impatrq/OIB_Sleep/Documentos/historias de usuarios .docx

Frente de la tarjeta | Reverso de la tarjeta
Comodidad Como Paciente que debe permanecer acostado por un largo tiempo Puedo usando materiales para que no se sientan los tubos de calefaccion y refrigeracion Para Permanecer cómodo durante la estancia en cama Criterios de Aceptación - Dado que quiero permanecer comodo en la cama - Cuando tenga que estar acostado - Entonces Los materiales de la cama van a ser óptimos y los tubos se pondrán en una posición para que no se sientan. | Detalles: - Los tubos deben ser flexibles para acomodarlos - La estructura de la cama tiene que mantenerse de buena calidad.
Display Como enfermero/a Puedo ver el estado del paciente Para poder controlar como esta Criterios de Aceptación - Dado que quiero ver como esta el paciente - Cuando lo este cuidando - Entonces puedo ver los datos de pulsaciones y temperatura en una display | Detalles: - Los datos se obtendran de la pico - Va a ser un display chico que pueda mostar los valores
Temperatura Como Persona mayor Puedo regular la temperatura del colchón Para ayudar a mi temperatura corporal que tiene menor regulación Criterios de Aceptación - Dado que necesito apoyo con la regulación de temperatura - Cuando duermo - Entonces La regulacion de temperatura del colchón me ayudara | Detalles: - La calefacción y refrigeración debe causar mínimo daño al colchón para que tenga una larga vida útil - La temperatura se poder regular automáticamente y manualmente
Diabetes Como persona con diabetes que afecta la circulación Puedo tener una temperatura elevada del colchón Para mejorar mi circulación en el cuerpo Criterios de Aceptación - Dado que necesito mejor regulación de circulación - Cuando estoy en la cama - Entonces temperatura aumentada va a ayudar con mi condición | Detalles: - La temperatura sera regulable por el usuario para su comodidad.

Pulsera

Como quiero que el colchon pueda ajustarse la temperatura por su cuenta

Puedo usar una pulsera con sensores

Para que mida el estado de sueño

Criterios de Aceptación

- Dado que un usuario no va a tener control mientras duerme
- Cuando esta dormido r
- Entonces una pulsera, usando sensores va a obtener mediciones y con esos poder calcular el estado para la regulacion de temperatura

Cambio de clima

Como persona en un clima cambiante

Puedo tener el colchón que se adapte al ambiente

Para que el cambio de clima no tenga efecto sobre mi sueño

Criterios de Aceptación

- Dado que el clima cambia radicalmente durante el año
- Cuando haya un cambio en el ambiente
- Entonces la cama adapta su temperatura para que ayudar con este cambio

Detalles:

- La pulsera no debe ser una molestia y debe mantenerse chica
- Tiene que poder comunicarse con el circuito principal

Detalles:

- Debe haber un sensor de temperatura fuera de la cama para obtener la temperatura ambiente
- Se debe comparar la temperatura de la cama y ambiente para obtener un buen resultado

Insomnio Como Puedo Dormir con mayor facilidad Para Poder rendir mejor en otros ámbito Criterios de Aceptación - Dado que Tengo insomnio - Cuando Es la hora de dormir - Entonces Regulo la temperatura a mi gusto para poder dormir | Detalles: - En el momento en el que se quede dormido el colchón prolongara el sueño rem - Se medirá su ritmo cardiaco para saber cuando entro el sueño rem
Eficiencia energética Como usuario que busca eficiencia energética Puedo hacer que el sistema apague la calefacción o refrigeración cuando no detecta presencia Para evitar gasto innecesario de energía. Criterios de Aceptación - Dado que quiero ahorrar energía - Cuando no se esté usando - Entonces poder detectar cuando no esté en uso y apagarse | Detalles: - Se va a necesitar un sensor para detectar cuando alguien esté en la cama o no
Control App Como usuario que viaja mucho Puedo controlar el sistema de Oib Sleep desde una app móvil Para dejarlo listo antes de llegar a casa Criterios de Aceptación - Dado que quiero mi cama calefaccionada - Cuando esté llegando a mi casa - Entonces podré dormir bien | Detalles: - Se va a tener que hacer una app para controlar el colchón de manera remota - Poder hacer que esto se pueda hacer desde la distancia
Facilidad Como Un usuario sin información Puedo Ver detalles del producto Para Mayor facilidad a la hora de usarlo Criterios de Aceptación - Dado que quiero tener informacion del producto - Cuando Busque comprar/usar el producto - Entonces Sabré como usarlo correctamente | Detalles: - Se van a crear presentación explicativas del producto - Se van a hacer manuales para el uso debido de el producto
