impatrq/OIB_Sleep/Latexx/Diagramas de bloques/presence_detector.png

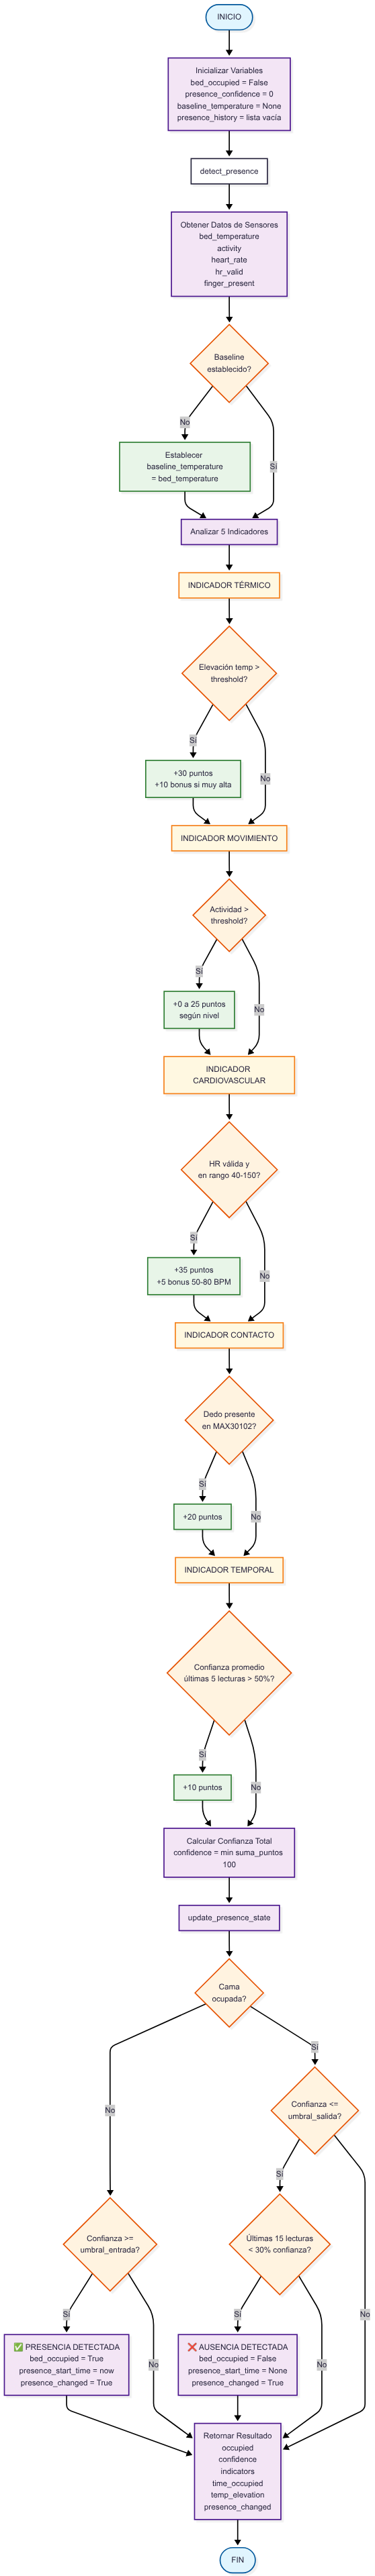
Latexx/Diagramas de bloques/presence_detector.png
