impatrq/OIB_Sleep/Latexx/fotos/foto.JPG

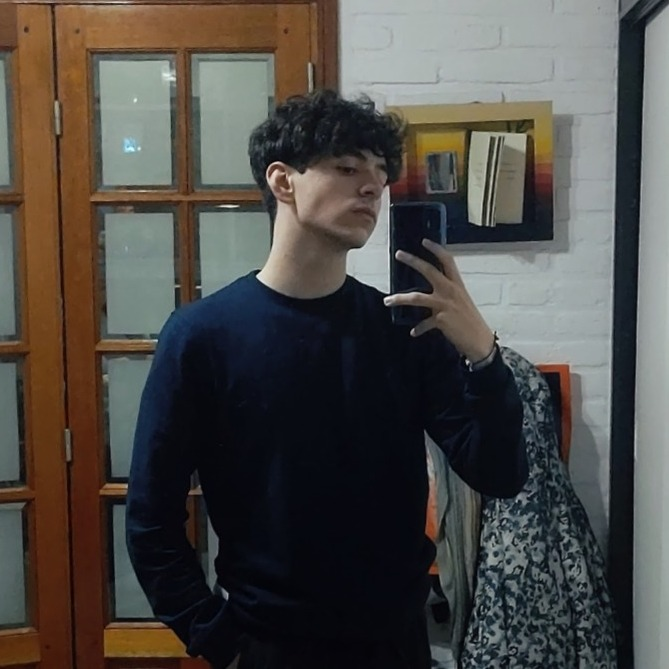
Latexx/fotos/foto.JPG
