impatrq/OIB_Sleep/Latexx/Modelos 3D/bedmodel.png

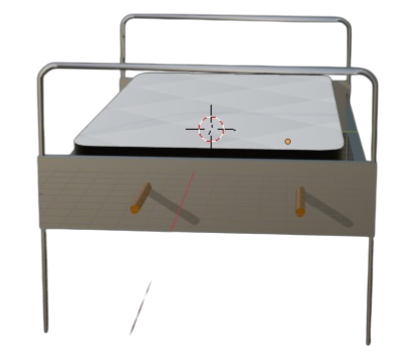
Latexx/Modelos 3D/bedmodel.png
