impatrq/OIB_Sleep/Latexx/programas/Blender.png

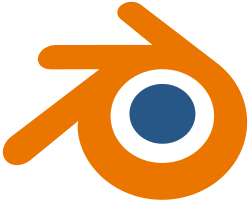
Latexx/programas/Blender.png
