impatrq/OIB_Sleep/Latexx/programas/Ibis.jpg

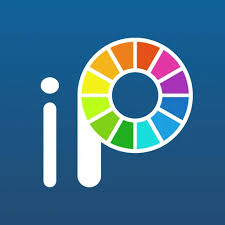
Latexx/programas/Ibis.jpg
