impatrq/OIB_Sleep/Latexx/programas/Overleaf.png

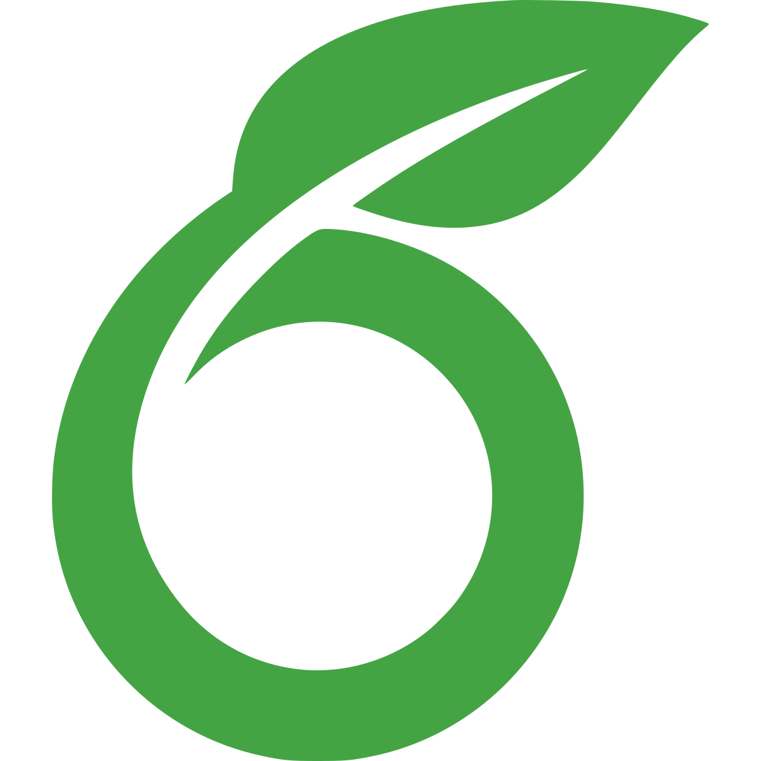
Latexx/programas/Overleaf.png
